cbb330/golf-glove/website/images/christian_reduced.jpg

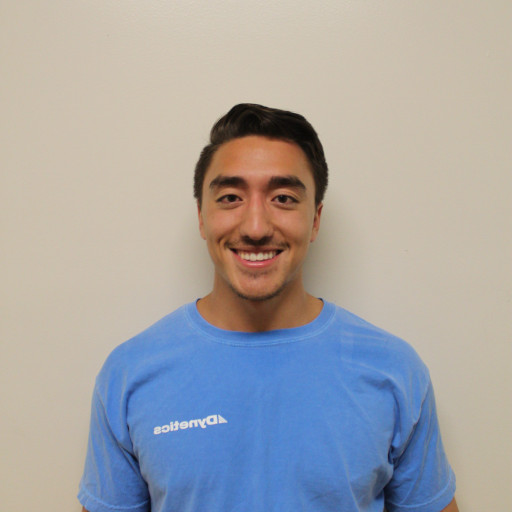
website/images/christian_reduced.jpg
