cbb330/golf-glove/website/images/christian_thumb.jpg

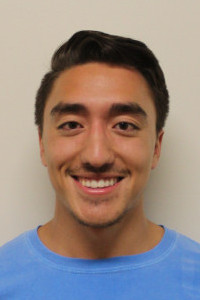
website/images/christian_thumb.jpg
