cbb330/golf-glove/website/images/glovespec.png

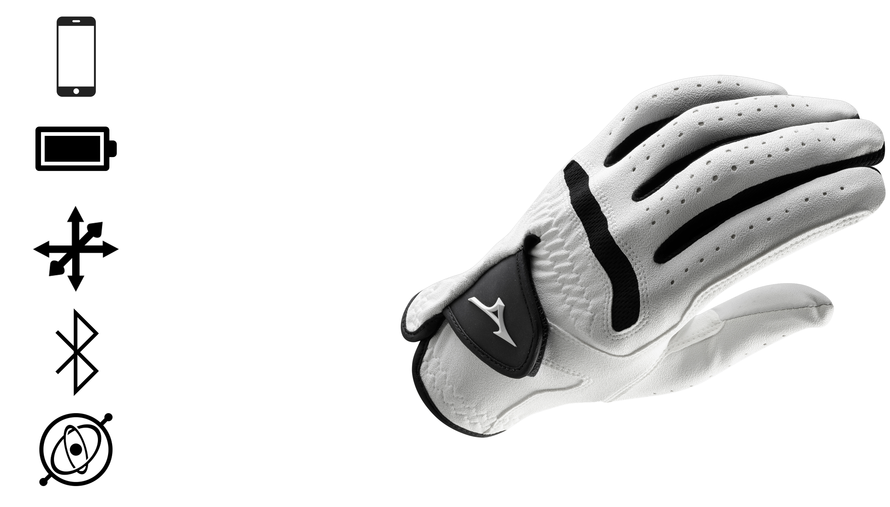
website/images/glovespec.png
