cbb330/golf-glove/website/images/jack_reduced.jpg

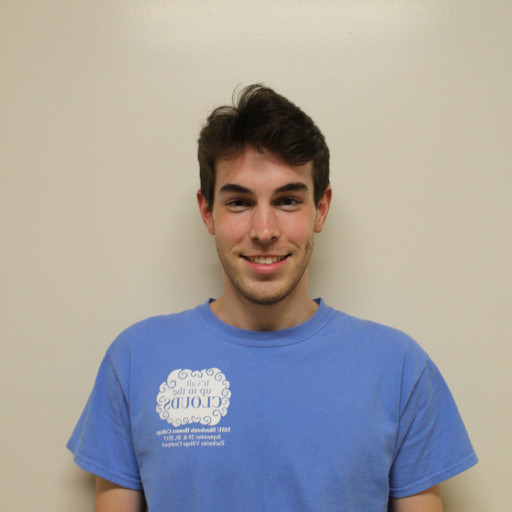
website/images/jack_reduced.jpg
