cbb330/golf-glove/website/images/jack_thumb.jpg

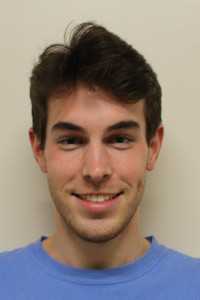
website/images/jack_thumb.jpg
