cbb330/golf-glove/website/images/landon_reduced.jpg

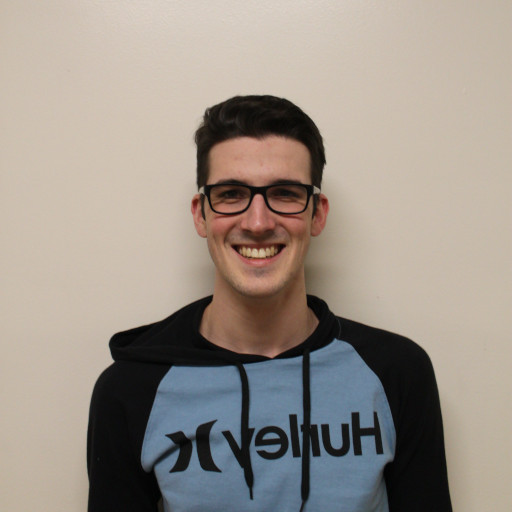
website/images/landon_reduced.jpg
