cbb330/golf-glove/website/images/landon_thumb.jpg

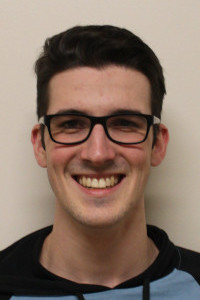
website/images/landon_thumb.jpg
