cbb330/golf-glove/website/images/screenshot_charts1.png

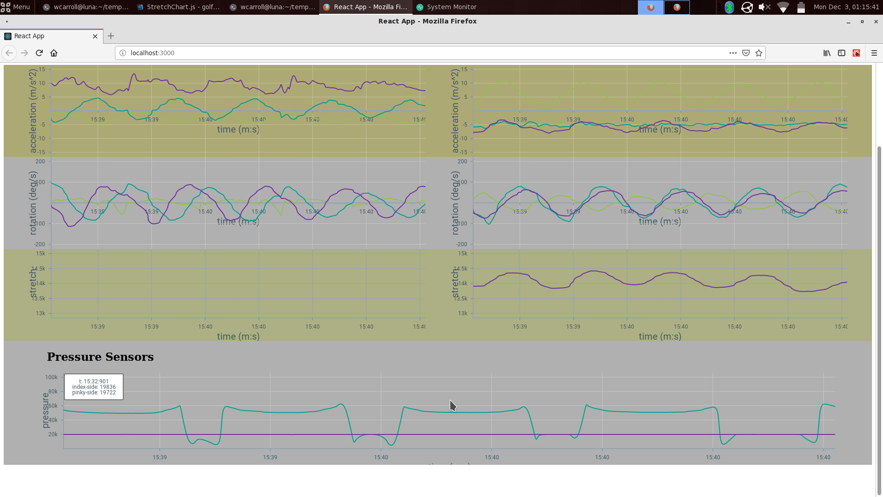
website/images/screenshot_charts1.png
