cbb330/golf-glove/website/images/spencer_reduced.jpg

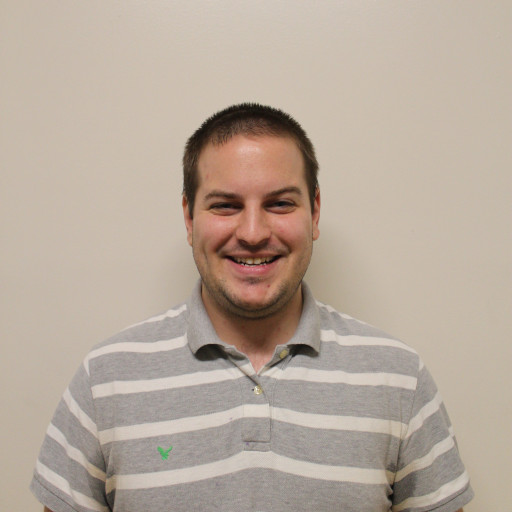
website/images/spencer_reduced.jpg
