cbb330/golf-glove/website/images/spencer_thumb.jpg

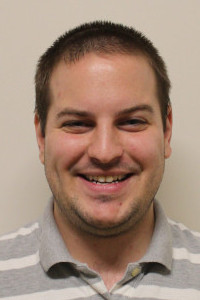
website/images/spencer_thumb.jpg
