cbb330/golf-glove/website/images/will_thumb.jpg

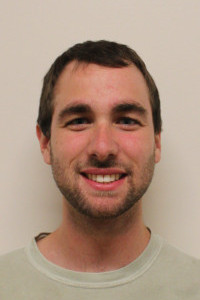
website/images/will_thumb.jpg
